VaeluxV/Modular-Train-Sim-Project/BlenderFiles/Modules/References/20251010132132_1.jpg

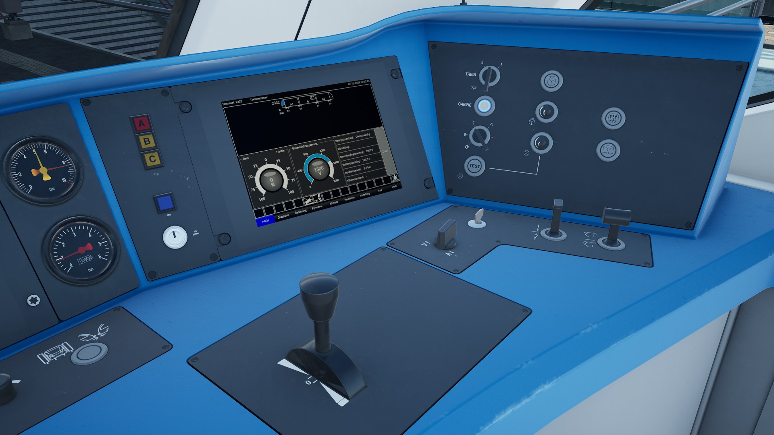
BlenderFiles/Modules/References/20251010132132_1.jpg
