VaeluxV/Modular-Train-Sim-Project/BlenderFiles/Modules/References/20251010132212_1.jpg

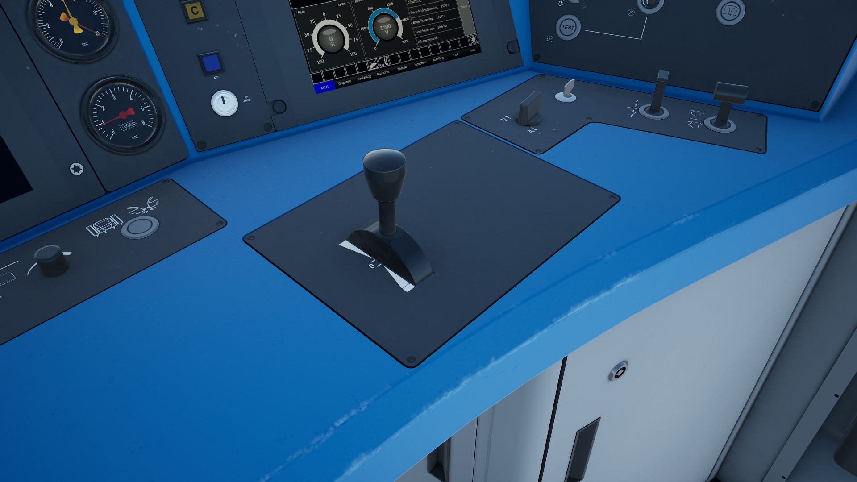
BlenderFiles/Modules/References/20251010132212_1.jpg
