VaeluxV/Modular-Train-Sim-Project/BlenderFiles/Modules/References/20251010132216_1.jpg

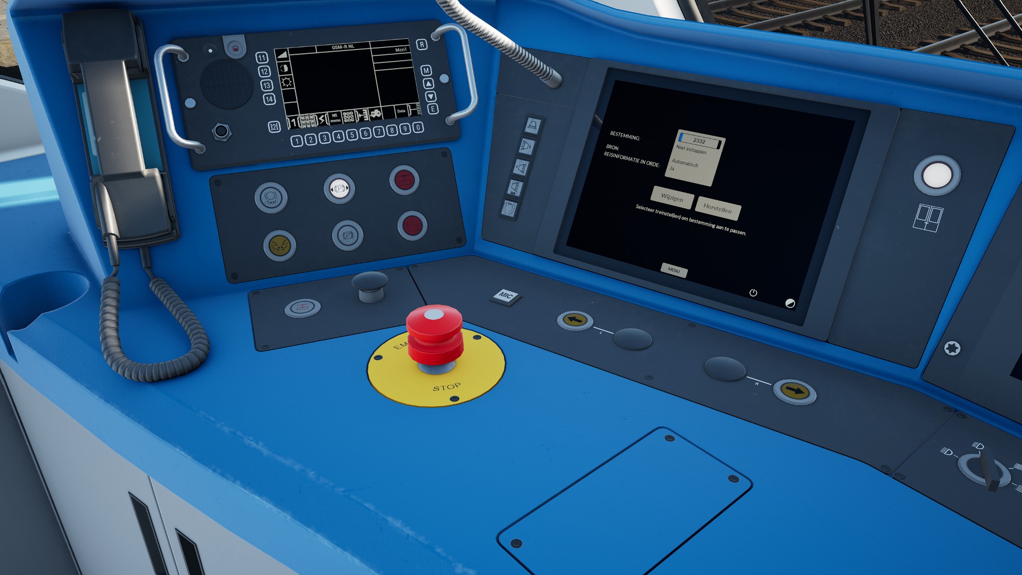
BlenderFiles/Modules/References/20251010132216_1.jpg
