VaeluxV/Modular-Train-Sim-Project/BlenderFiles/Modules/References/20251010132233_2.jpg

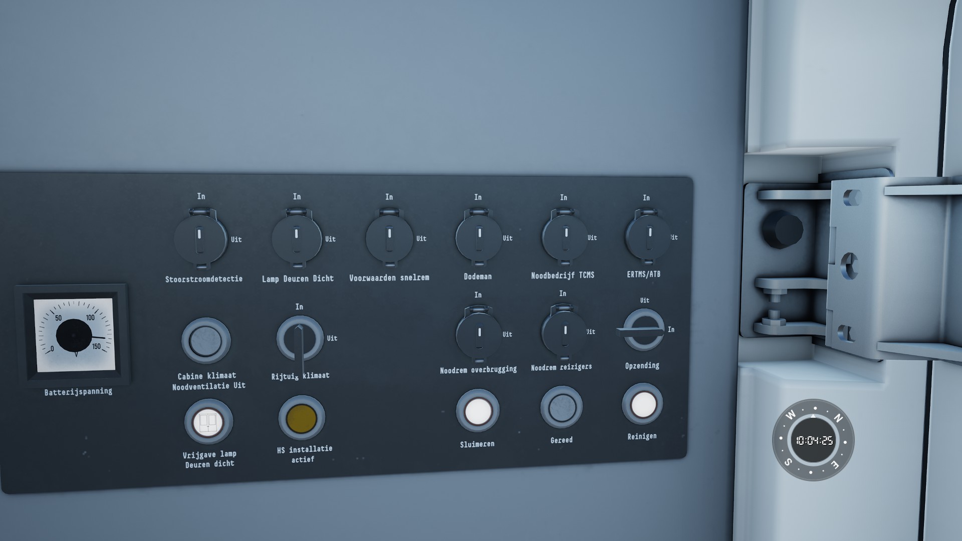
BlenderFiles/Modules/References/20251010132233_2.jpg
