VaeluxV/Modular-Train-Sim-Project/BlenderFiles/Modules/References/20251010132505_1.jpg

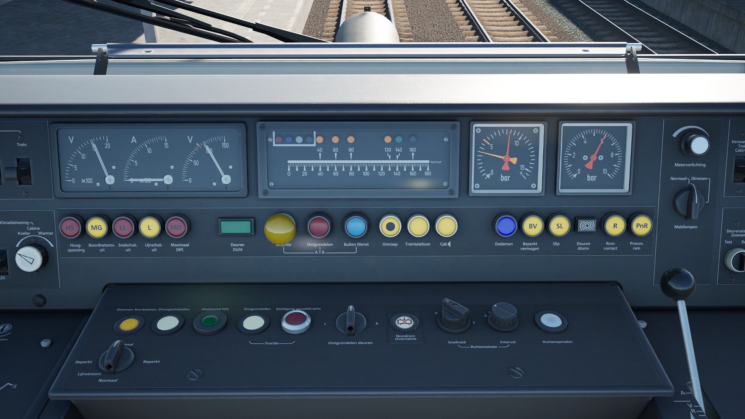
BlenderFiles/Modules/References/20251010132505_1.jpg
