VaeluxV/Modular-Train-Sim-Project/BlenderFiles/Modules/References/20251010132508_1.jpg

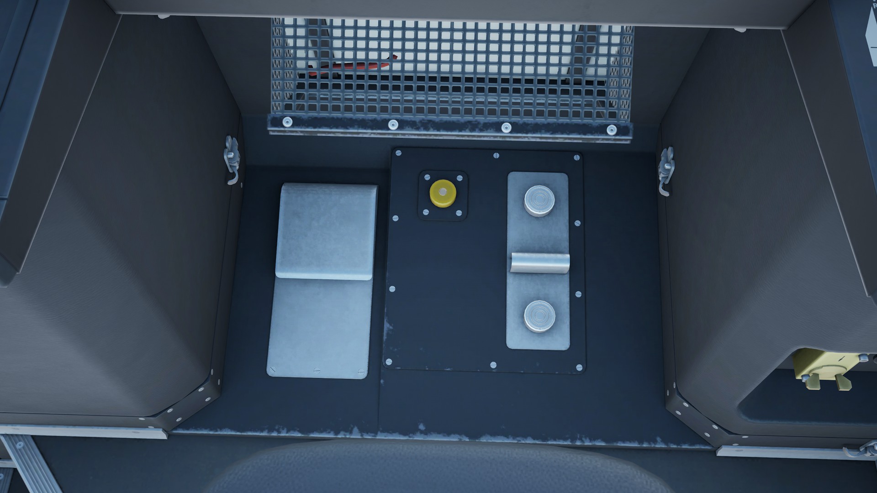
BlenderFiles/Modules/References/20251010132508_1.jpg
