VaeluxV/Modular-Train-Sim-Project/BlenderFiles/Modules/STLS/TEST-STL-0.13.x/Lever-Base-Standard-No-Magnet-Layout-TS-v0.13.3.stl

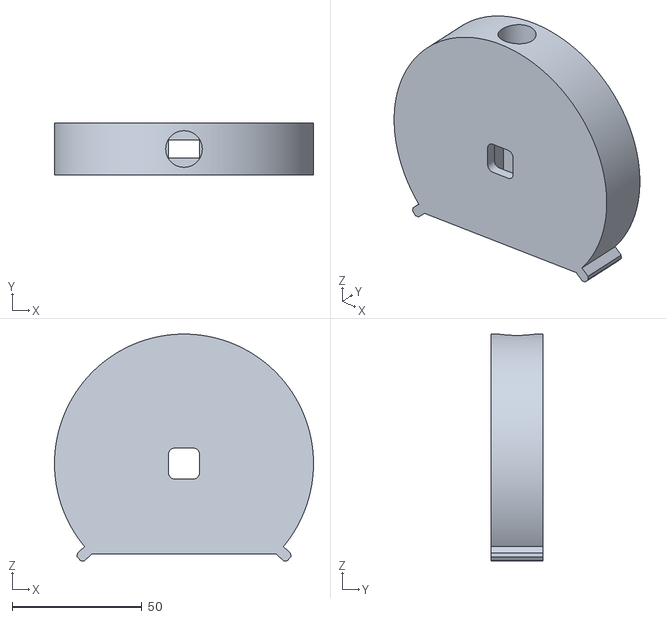
[picture p43: CAD file, 2025-12-05]
BlenderFiles/Modules/STLS/TEST-STL-0.13.x/Lever-Base-Standard-No-Magnet-Layout-TS-v0.13.3.stl
100.0 x 20.0 x 87.6
