VaeluxV/Modular-Train-Sim-Project/BlenderFiles/Modules/STLS/TEST-STL-0.14.x/0.14.0/Lever-Shaft-Friction-Attachment-TSv0.14.0.stl

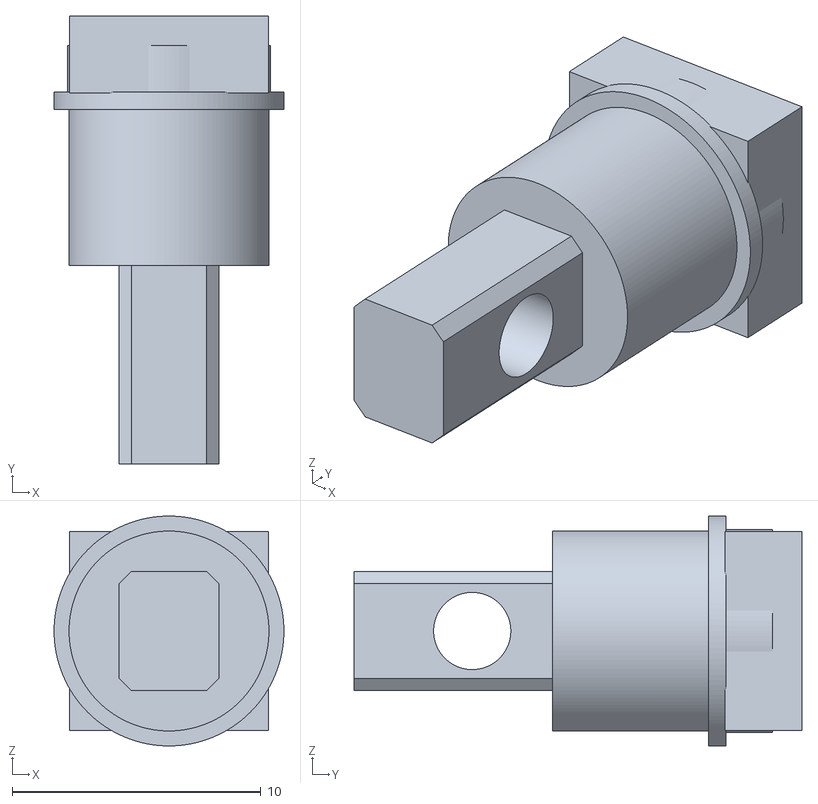
[picture p44: CAD file, 2025-12-11]
BlenderFiles/Modules/STLS/TEST-STL-0.14.x/0.14.0/Lever-Shaft-Friction-Attachment-TSv0.14.0.stl
9.24 x 18.0 x 9.24
