VaeluxV/Modular-Train-Sim-Project/BlenderFiles/STLs/v0.10.5/levers_standard/handle_top_long_no_button_standard_lever-MTSP-v0.10.5.stl

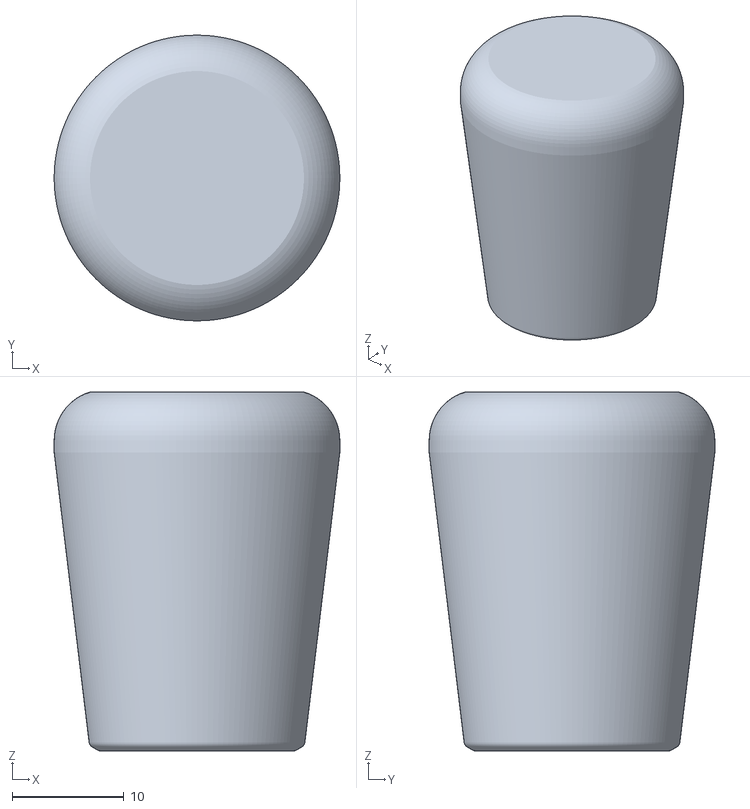
[picture p45: CAD file, 2025-04-10]
BlenderFiles/STLs/v0.10.5/levers_standard/handle_top_long_no_button_standard_lever-MTSP-v0.10.5.stl
25.5 x 25.5 x 32.1
