VaeluxV/Modular-Train-Sim-Project/BlenderFiles/Modules/STLS/TEST-STL-0.12/TS-Bottom-Lever-Module-v0.12.0.stl

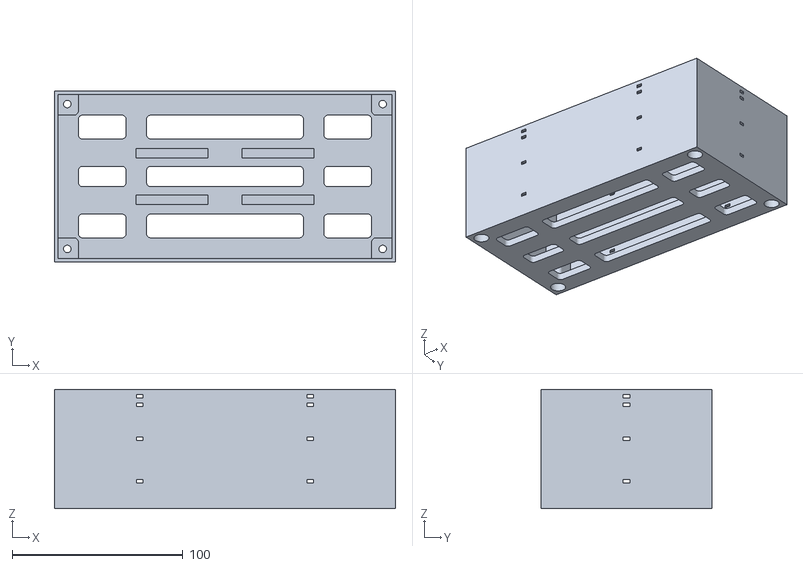
[picture p46: CAD file, 2025-12-02]
BlenderFiles/Modules/STLS/TEST-STL-0.12/TS-Bottom-Lever-Module-v0.12.0.stl
200.0 x 100.0 x 70.0
