VaeluxV/Modular-Train-Sim-Project/BlenderFiles/Modules/STLS/TEST-STL-0.14.x/0.14.0/Lever-Base-Middle-Generic-TSv0.14.0.stl

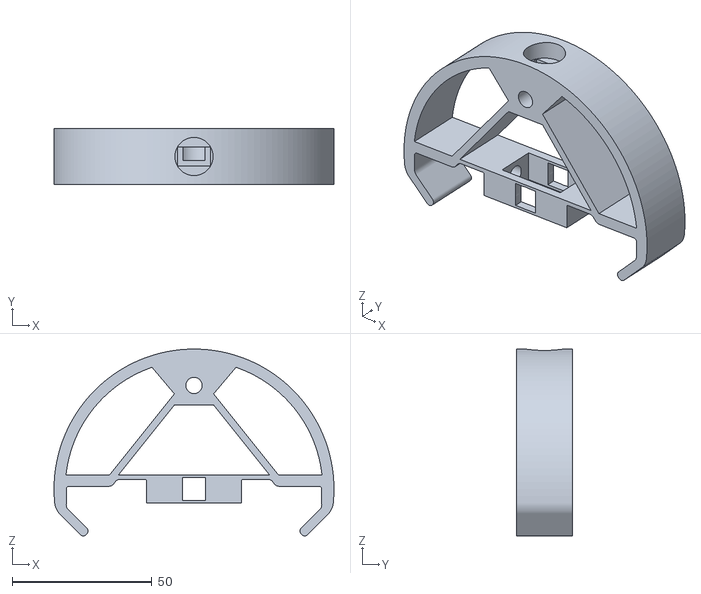
[picture p48: CAD file, 2025-12-11]
BlenderFiles/Modules/STLS/TEST-STL-0.14.x/0.14.0/Lever-Base-Middle-Generic-TSv0.14.0.stl
100.0 x 20.0 x 66.7
