VaeluxV/Modular-Train-Sim-Project/BlenderFiles/STLs/v0.10.5/levers_standard/handle_top_standard_lever-MTSP-v0.10.5.stl

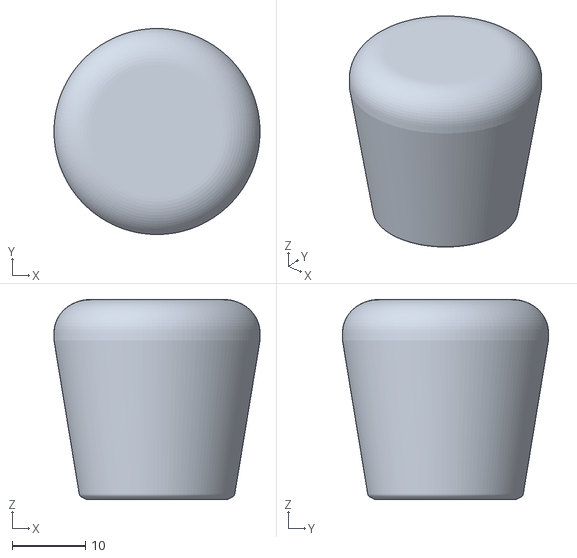
[picture p49: CAD file, 2025-04-10]
BlenderFiles/STLs/v0.10.5/levers_standard/handle_top_standard_lever-MTSP-v0.10.5.stl
28.1 x 28.1 x 27.3
