VaeluxV/Modular-Train-Sim-Project/BlenderFiles/Modules/STLS/TEST-STL-0.11/Magnet-Connector-TS-v0.11.3.stl

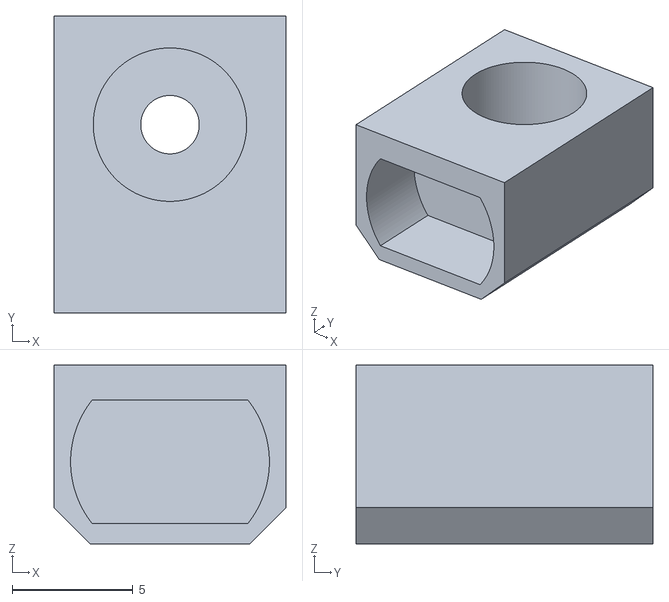
[picture p50: CAD file, 2025-10-11]
BlenderFiles/Modules/STLS/TEST-STL-0.11/Magnet-Connector-TS-v0.11.3.stl
9.60 x 12.3 x 7.40
