VaeluxV/Modular-Train-Sim-Project/BlenderFiles/Modules/STLS/TEST-STL-0.12/TS-Test-v0.12.0.stl

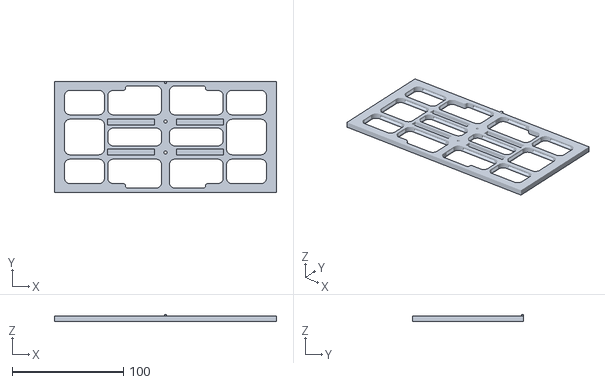
[picture p51: CAD file, 2025-12-01]
BlenderFiles/Modules/STLS/TEST-STL-0.12/TS-Test-v0.12.0.stl
200.0 x 100.0 x 6.50
