VaeluxV/Modular-Train-Sim-Project/BlenderFiles/STLs/v0.10.5/levers_standard/handle_base_long_lever-MTSP-v0.10.5.stl

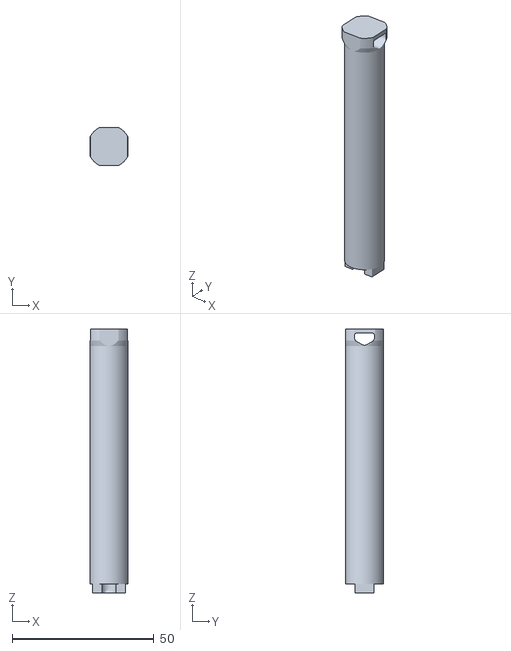
[picture p53: CAD file, 2025-04-10]
BlenderFiles/STLs/v0.10.5/levers_standard/handle_base_long_lever-MTSP-v0.10.5.stl
13.4 x 13.4 x 93.1
