VaeluxV/Modular-Train-Sim-Project/BlenderFiles/Modules/STLS/TEST-STL-0.13.x/Lever-Shaft-Attachment-TS-v0.13.3.stl

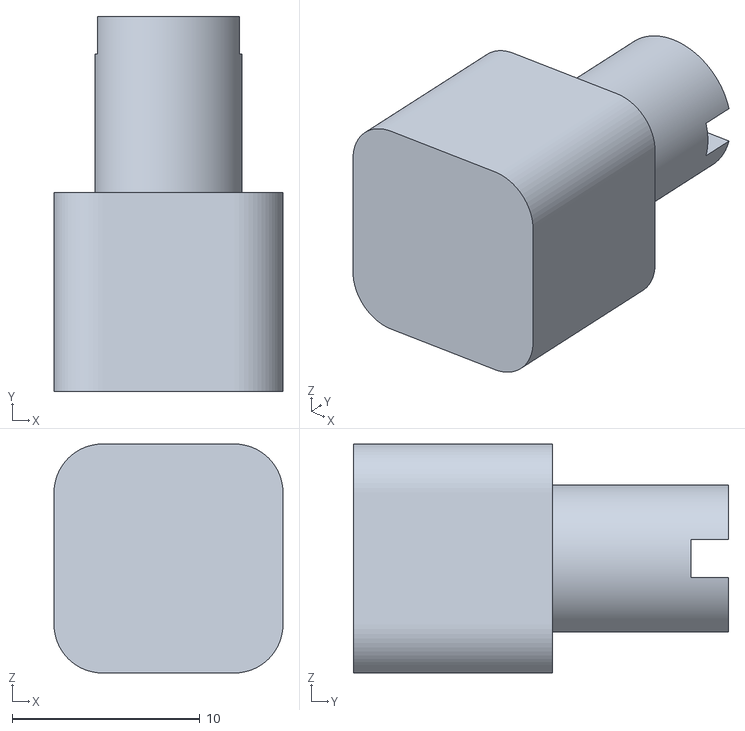
[picture p54: CAD file, 2025-12-04]
BlenderFiles/Modules/STLS/TEST-STL-0.13.x/Lever-Shaft-Attachment-TS-v0.13.3.stl
12.2 x 20.0 x 12.2
