VaeluxV/Modular-Train-Sim-Project/BlenderFiles/Modules/STLS/TEST-STL-0.14.x/0.14.0/Lever-Shaft-Friction-Part-TSv0.14.0.stl

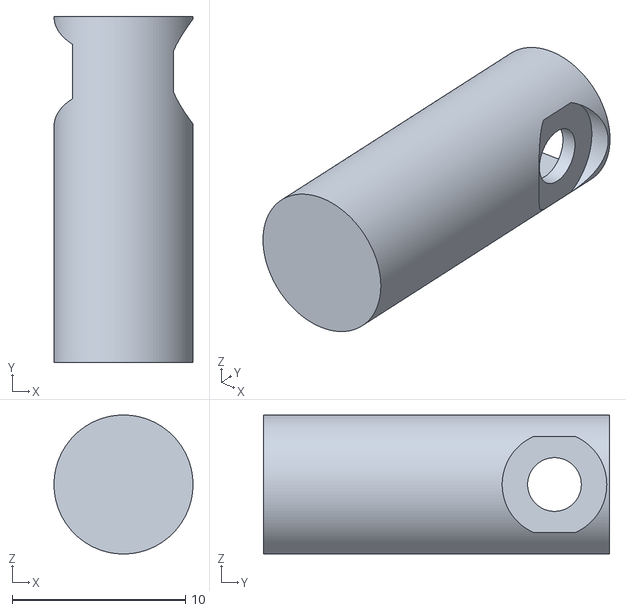
[picture p55: CAD file, 2025-12-11]
BlenderFiles/Modules/STLS/TEST-STL-0.14.x/0.14.0/Lever-Shaft-Friction-Part-TSv0.14.0.stl
8.03 x 20.0 x 8.03
