VaeluxV/Modular-Train-Sim-Project/BlenderFiles/Modules/STLS/TEST-STL-0.11/Spring-Lever-TS-v0.11.4.stl

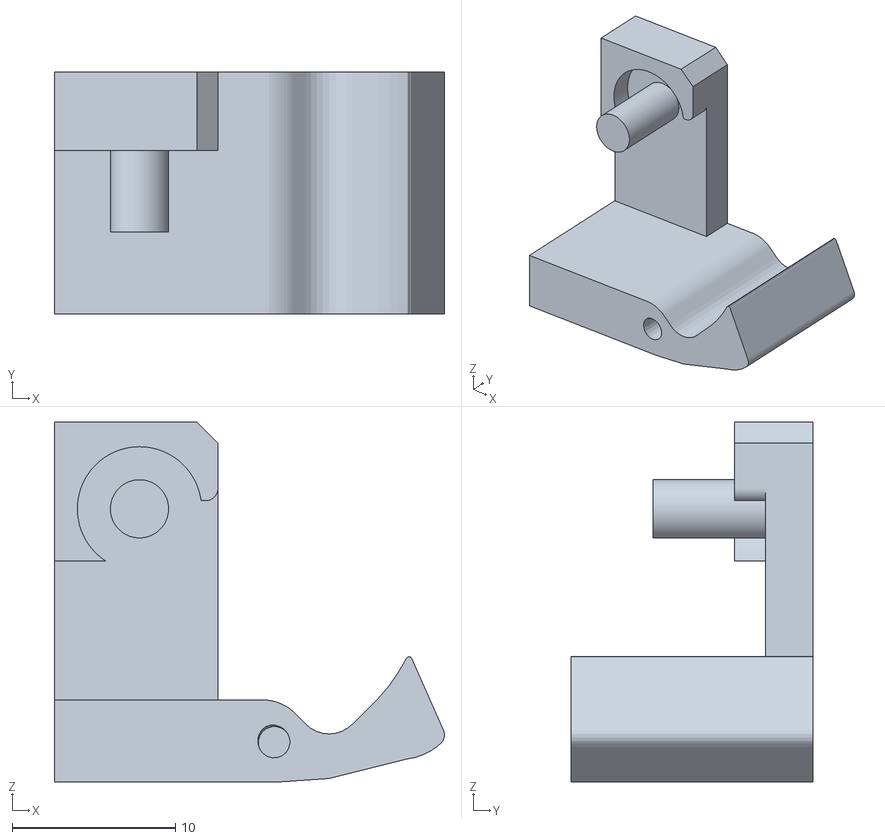
[picture p56: CAD file, 2025-10-11]
BlenderFiles/Modules/STLS/TEST-STL-0.11/Spring-Lever-TS-v0.11.4.stl
23.9 x 14.8 x 22.0
