VaeluxV/Modular-Train-Sim-Project/BlenderFiles/Modules/STLS/TEST-STL-0.13.x/Lever-Side-Hall-Magnet-Attachment-TS-v0.13.3.stl

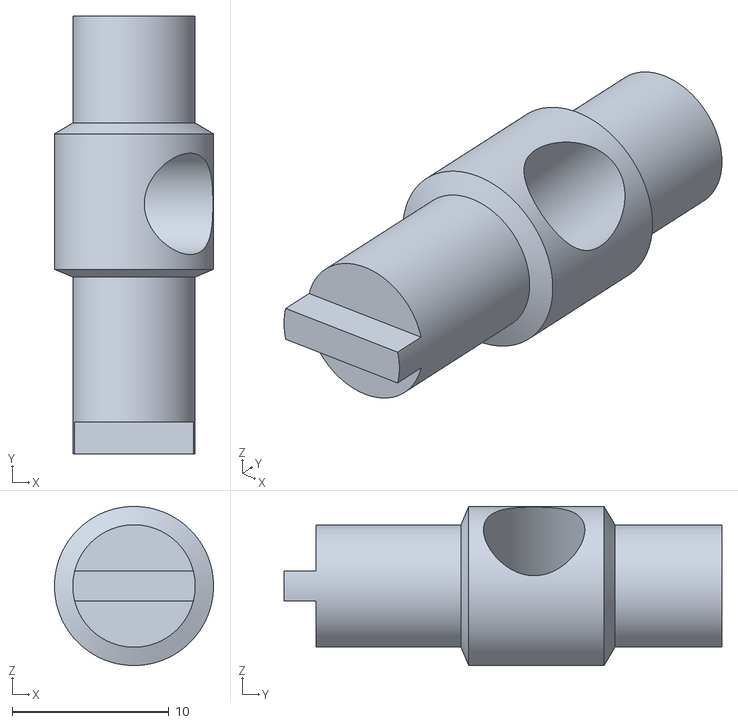
[picture p57: CAD file, 2025-12-04]
BlenderFiles/Modules/STLS/TEST-STL-0.13.x/Lever-Side-Hall-Magnet-Attachment-TS-v0.13.3.stl
10.2 x 28.0 x 10.2
