VaeluxV/Modular-Train-Sim-Project/BlenderFiles/Modules/STLS/TEST-STL-0.14.x/0.14.0/Lever-Base-Side-Notched-Center-Ends-TSv0.14.0.stl

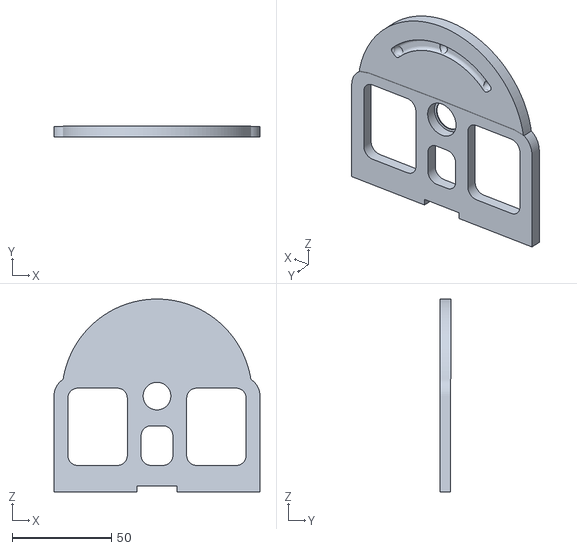
[picture p58: CAD file, 2025-12-11]
BlenderFiles/Modules/STLS/TEST-STL-0.14.x/0.14.0/Lever-Base-Side-Notched-Center-Ends-TSv0.14.0.stl
104.0 x 5.80 x 97.4
