VaeluxV/Modular-Train-Sim-Project/BlenderFiles/STLs/v0.10.5/levers_standard/unique_side_combined_throttle_brake_lever-MTSP-v0.9.8.stl

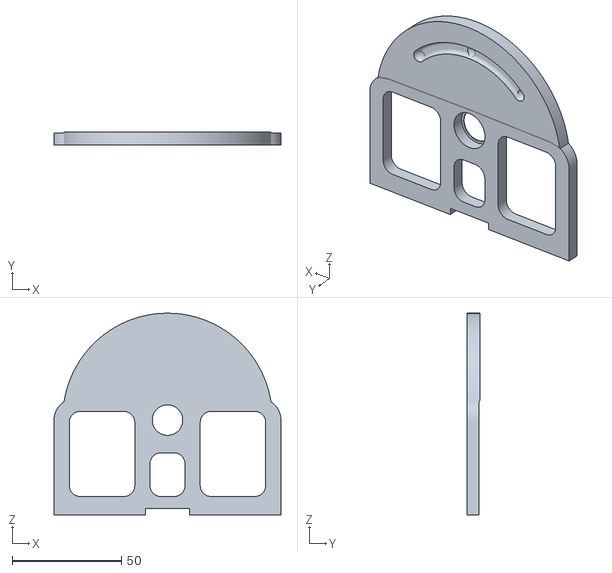
[picture p59: CAD file, 2024-11-03]
BlenderFiles/STLs/v0.10.5/levers_standard/unique_side_combined_throttle_brake_lever-MTSP-v0.9.8.stl
104.0 x 5.80 x 92.4
