VaeluxV/Modular-Train-Sim-Project/BlenderFiles/Modules/STLS/TEST-STL-0.13.x/Lever-Shaft-Friction-TS-v0.13.3.stl

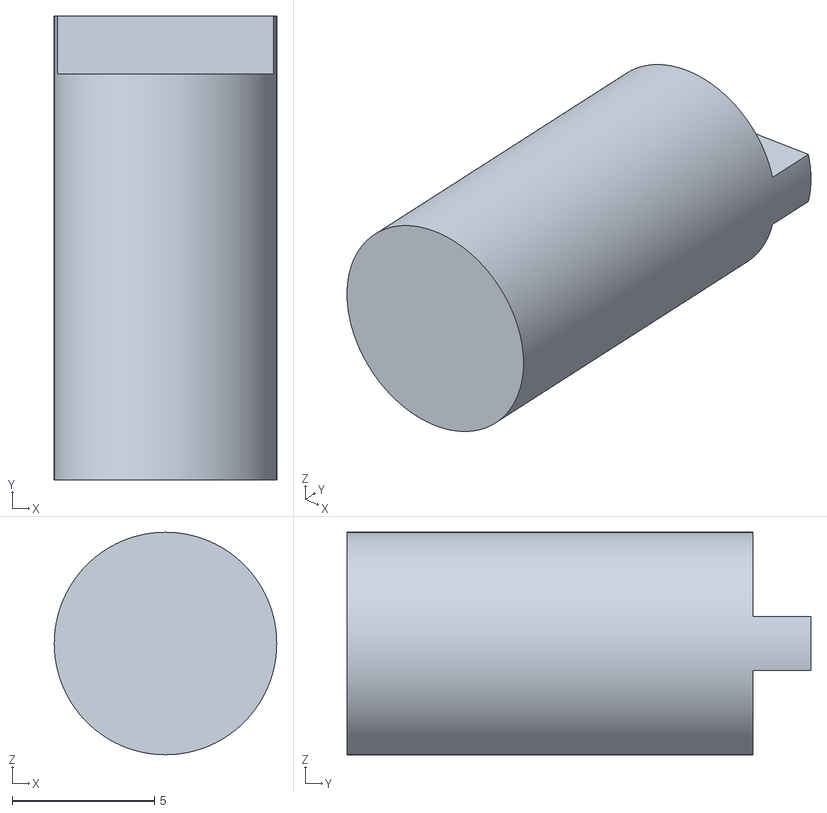
[picture p60: CAD file, 2025-12-04]
BlenderFiles/Modules/STLS/TEST-STL-0.13.x/Lever-Shaft-Friction-TS-v0.13.3.stl
7.82 x 16.3 x 7.82
