VaeluxV/Modular-Train-Sim-Project/BlenderFiles/Modules/STLS/TEST-STL-0.11/Shaft-Connector-TS-v0.11.0.stl

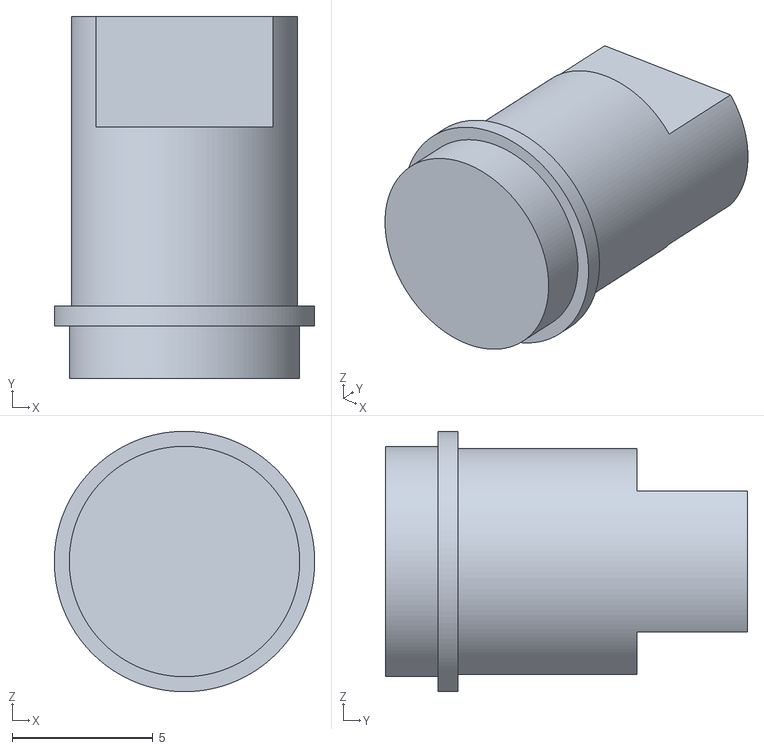
[picture p61: CAD file, 2025-10-11]
BlenderFiles/Modules/STLS/TEST-STL-0.11/Shaft-Connector-TS-v0.11.0.stl
9.24 x 12.8 x 9.24
