VaeluxV/Modular-Train-Sim-Project/BlenderFiles/Modules/STLS/TEST-STL-0.11/Experimental-TS-v0.11.5.3mf

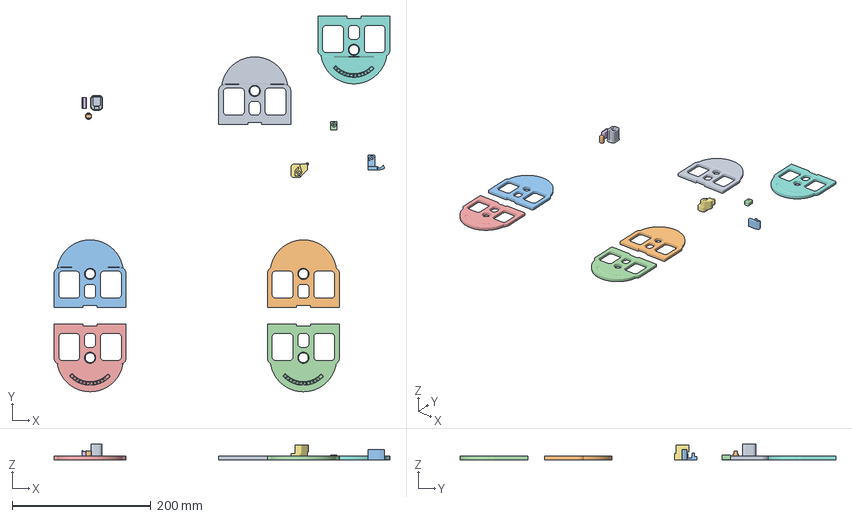
[picture p64: CAD file, 2025-10-11]
BlenderFiles/Modules/STLS/TEST-STL-0.11/Experimental-TS-v0.11.5.3mf
483.9 x 540.9 x 23.0 mm
Sensor-holder-bottom-TS-v0.11.0.stl
Side-Lever-No-Indents-Flat-TS-v0.11.5.stl
Side-Lever-No-Indents-TS-v0.11.5.stl
Side-Lever-Indents-Flat-TS-v0.11.5.stl
Side-Lever-Indents-TS-v0.11.5.stl
Sensor-holder-TS-v0.11.0.stl
Spring-Base-TS-v0.11.4.stl
Side-Lever-Indents-TS-v0.11.4.stl
Side-Lever-No-Indents-TS-v0.11.4.stl
Shaft-Connector-TS-v0.11.0.stl
Spring-Lever-TS-v0.11.4.stl
Magnet-Connector-TS-v0.11.3.stl
