VaeluxV/Modular-Train-Sim-Project/BlenderFiles/Modules/STLS/TEST-STL-0.13.x/Lever-Side-FrictionShaft-Part-TS-v0.13.3.stl

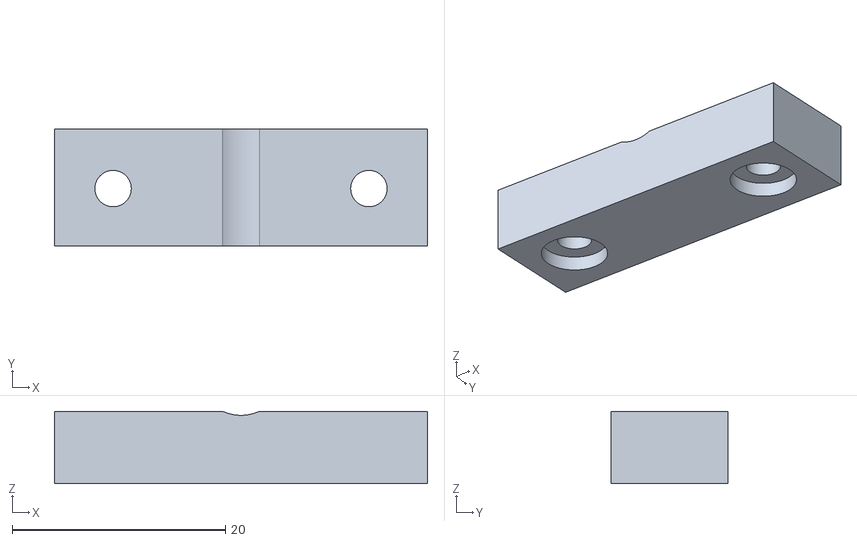
[picture p65: CAD file, 2025-12-04]
BlenderFiles/Modules/STLS/TEST-STL-0.13.x/Lever-Side-FrictionShaft-Part-TS-v0.13.3.stl
35.0 x 11.0 x 6.80
