VaeluxV/Modular-Train-Sim-Project/BlenderFiles/Modules/STLS/TEST-STL-0.14.x/0.14.0/Lever-Shaft-Fricton-Extrusion-Part-TSv0.14.0.stl

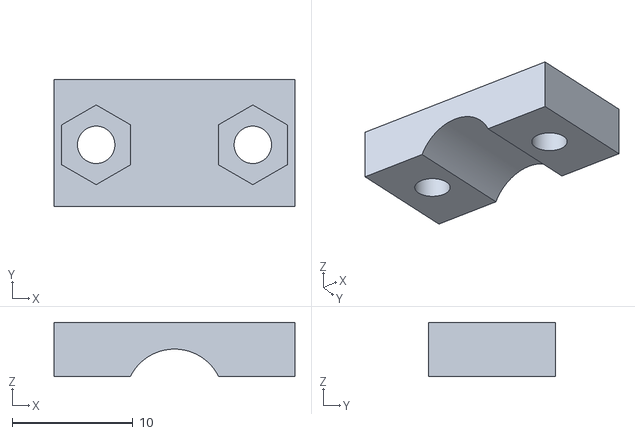
[picture p66: CAD file, 2025-12-11]
BlenderFiles/Modules/STLS/TEST-STL-0.14.x/0.14.0/Lever-Shaft-Fricton-Extrusion-Part-TSv0.14.0.stl
20.0 x 10.5 x 4.50
