VaeluxV/Modular-Train-Sim-Project/BlenderFiles/Modules/STLS/TEST-STL-0.13.x/Lever-Side-Hall-Sensor-Attachment-TS-v0.13.3.stl

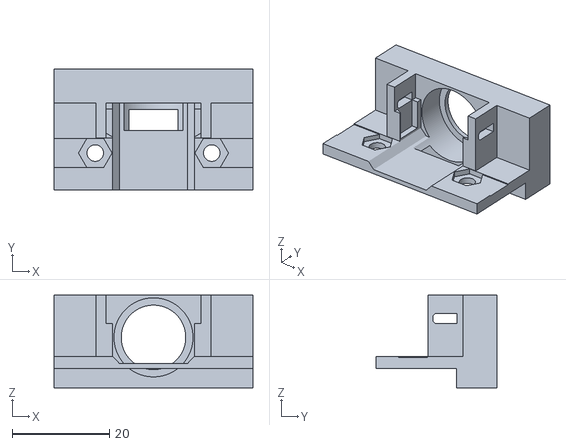
[picture p67: CAD file, 2025-12-04]
BlenderFiles/Modules/STLS/TEST-STL-0.13.x/Lever-Side-Hall-Sensor-Attachment-TS-v0.13.3.stl
41.0 x 24.9 x 19.1
