VaeluxV/Modular-Train-Sim-Project/BlenderFiles/Modules/STLS/TEST-STL-0.13.x/Lever-FrictionShaft-OneSide-TS-v0.13.3.stl

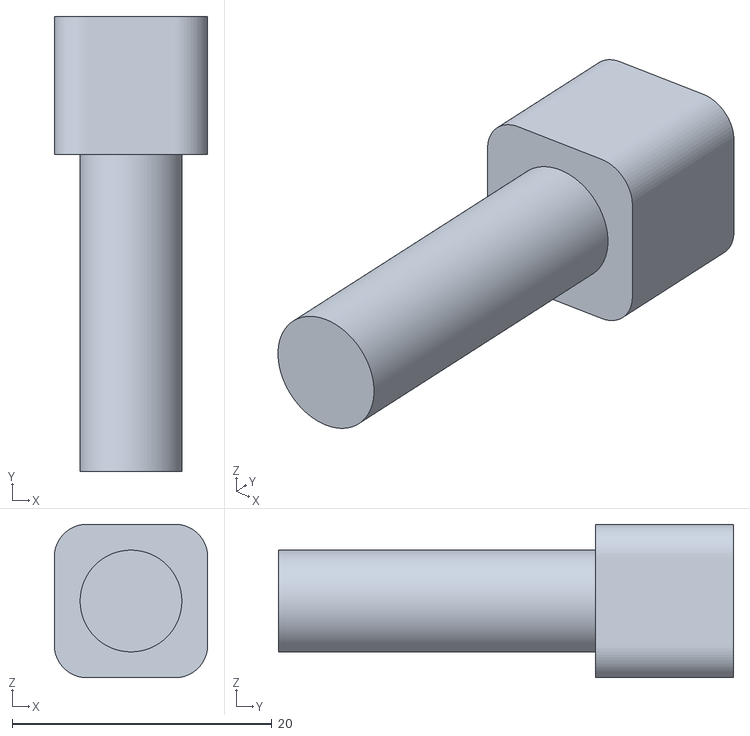
[picture p68: CAD file, 2025-12-04]
BlenderFiles/Modules/STLS/TEST-STL-0.13.x/Lever-FrictionShaft-OneSide-TS-v0.13.3.stl
11.8 x 35.0 x 11.8
