VaeluxV/Modular-Train-Sim-Project/BlenderFiles/Modules/STLS/TEST-STL-0.14.x/0.14.0/Lever-Shaft-Fricton-Extrusion-TSv0.14.0.stl

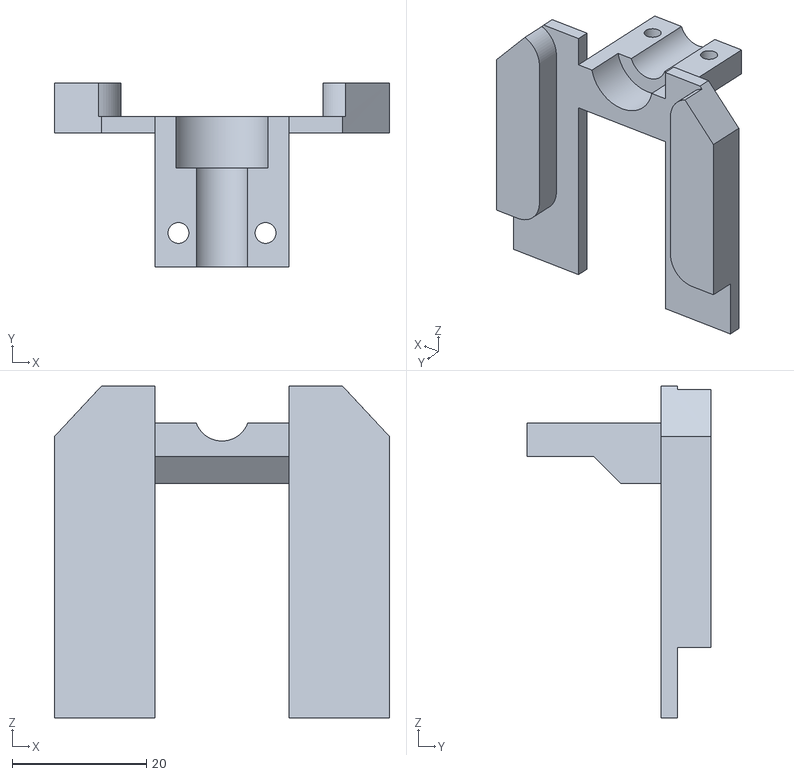
[picture p69: CAD file, 2025-12-11]
BlenderFiles/Modules/STLS/TEST-STL-0.14.x/0.14.0/Lever-Shaft-Fricton-Extrusion-TSv0.14.0.stl
50.0 x 27.5 x 49.5
