VaeluxV/Modular-Train-Sim-Project/BlenderFiles/Modules/STLS/TEST-STL-0.13.x/Lever-Base-TS-v0.13.3.stl

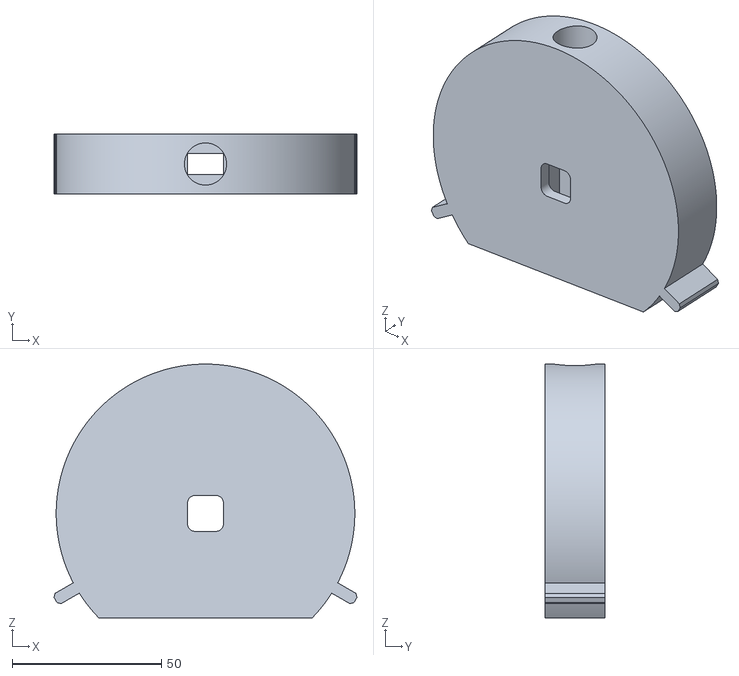
[picture p70: CAD file, 2025-12-04]
BlenderFiles/Modules/STLS/TEST-STL-0.13.x/Lever-Base-TS-v0.13.3.stl
101.5 x 20.0 x 85.0
