VaeluxV/Modular-Train-Sim-Project/BlenderFiles/Modules/STLS/TEST-STL-0.14.x/0.14.0/Lever-Handle-Button-TSv0.14.0.stl

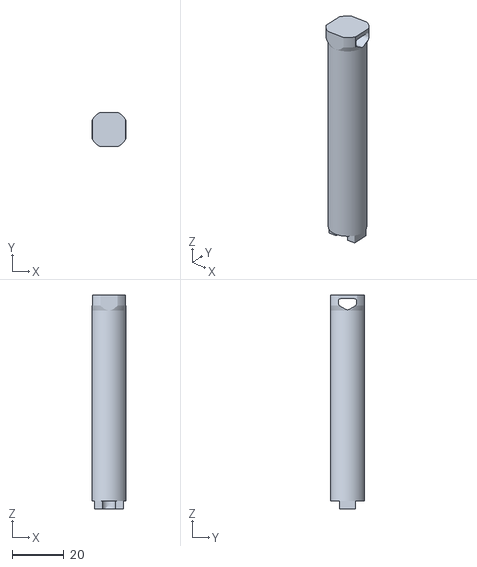
[picture p71: CAD file, 2025-12-11]
BlenderFiles/Modules/STLS/TEST-STL-0.14.x/0.14.0/Lever-Handle-Button-TSv0.14.0.stl
13.4 x 13.4 x 83.1
