VaeluxV/Modular-Train-Sim-Project/BlenderFiles/Modules/STLS/TEST-STL-0.13.x/Lever-Side-Normal-TS-v0.13.3.stl

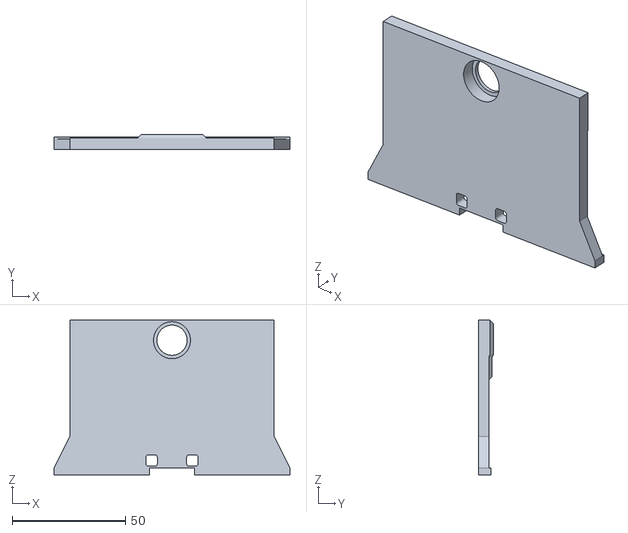
[picture p72: CAD file, 2025-12-04]
BlenderFiles/Modules/STLS/TEST-STL-0.13.x/Lever-Side-Normal-TS-v0.13.3.stl
104.0 x 6.50 x 68.3
