VaeluxV/Modular-Train-Sim-Project/BlenderFiles/Modules/STLS/TEST-STL-0.13.x/Lever-Shaft-OneSide-TS-v0.13.3.stl

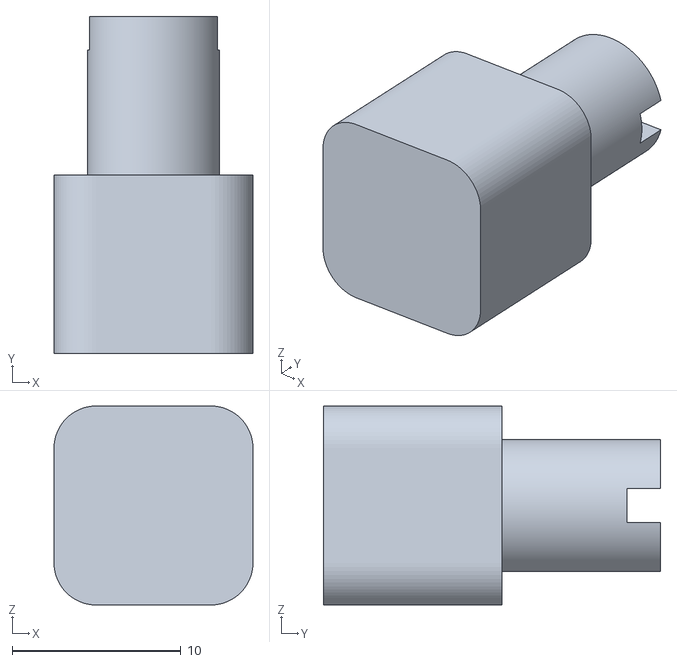
[picture p73: CAD file, 2025-12-03]
BlenderFiles/Modules/STLS/TEST-STL-0.13.x/Lever-Shaft-OneSide-TS-v0.13.3.stl
11.8 x 20.0 x 11.8
